davide0707/lora-bidirezionale/pcb/Board Images/Bottom Side PCB.png

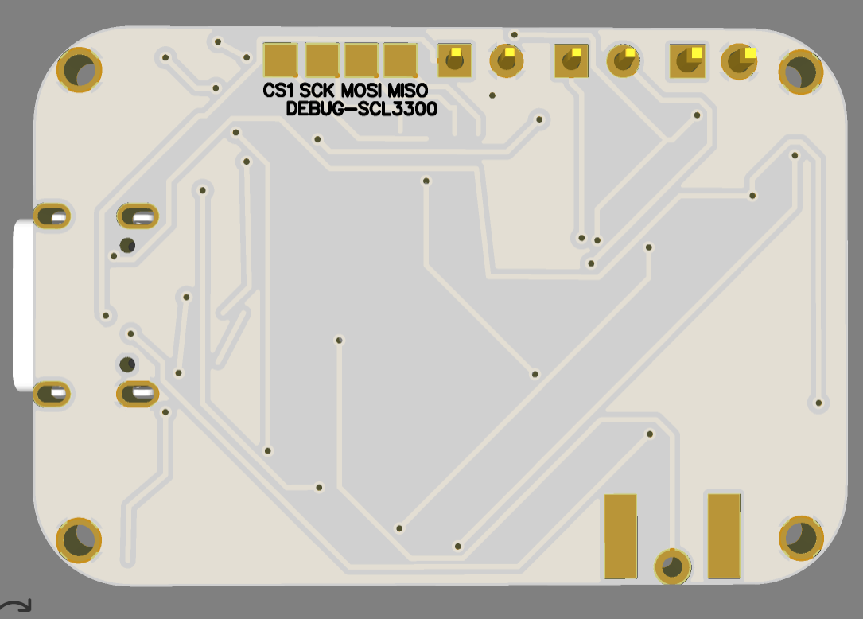
pcb/Board Images/Bottom Side PCB.png
