davide0707/lora-bidirezionale/PROVA PROGETTO/Wio-E5-mini_lorawan_end_node-main/Wio-E5-mini_lorawan_end_node-main/LoRaWAN_End_Node_WIOE5LEmini_FW1_3_1/LoRaWAN/App/lora_app.c

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

/* Includes ------------------------------------------------------------------*/
#include "platform.h"
#include "sys_app.h"
#include "lora_app.h"
#include "stm32_seq.h"
#include "stm32_timer.h"
#include "utilities_def.h"
#include "app_version.h"
#include "lorawan_version.h"
#include "subghz_phy_version.h"
#include "lora_info.h"
#include "LmHandler.h"
#include "adc_if.h"
#include "CayenneLpp.h"
#include "sys_sensors.h"
#include "flash_if.h"


/* USER CODE BEGIN Includes */
#include "scl3300.h"
#include <stdio.h>
#include <string.h>
#include <stdlib.h>
/* USER CODE END Includes */

/* External variables ---------------------------------------------------------*/
/* USER CODE BEGIN EV */
extern SCL3300_t sensor;
#include "lora_app.h"
#include "sys_app.h"
#include "scl3300.h"
#include "usart.h"


float offset_X = 0.0f;
float offset_Y = 0.0f;
float offset_Z = 0.0f;
// Filtro EMA
static float emaX = 0, emaY = 0, emaZ = 0, emaT = 0;
static bool ema_initialized = false;
#define EMA_ALPHA 0.2f  // coefficiente di smoothing (0.1–0.3)

/* USER CODE END EV */

/**
  * @brief LoRa State Machine states
  */
typedef enum TxEventType_e
{
  /**
    * @brief Appdata Transmission issue based on timer every TxDutyCycleTime
    */
  TX_ON_TIMER,
  /**
    * @brief Appdata Transmission external event plugged on OnSendEvent( )
    */
  TX_ON_EVENT
} TxEventType_t;

/**
  * LEDs period value of the timer in ms
  */
#define LED_PERIOD_TIME 500

/**
  * Join switch period value of the timer in ms
  */
#define JOIN_TIME 2000

/*---------------------------------------------------------------------------*/
/*                             LoRaWAN NVM configuration                     */
/*---------------------------------------------------------------------------*/
/**
  * @brief LoRaWAN NVM Flash address
  * @note last 2 sector of a 128kBytes device
  */
#define LORAWAN_NVM_BASE_ADDRESS                    ((void *)0x0803F000UL)

/* USER CODE BEGIN PD */
static const char *slotStrings[] = { "1", "2", "C", "C_MC", "P", "P_MC" };
/* USER CODE END PD */

/**
  * @brief  LoRa End Node send request
  */
static void SendTxData(void);

/**
  * @brief  TX timer callback function
  * @param  context ptr of timer context
  */
static void OnTxTimerEvent(void *context);

/**
  * @brief  join event callback function
  * @param  joinParams status of join
  */
static void OnJoinRequest(LmHandlerJoinParams_t *joinParams);

/**
  * @brief callback when LoRaWAN application has sent a frame
  * @brief  tx event callback function
  * @param  params status of last Tx
  */
static void OnTxData(LmHandlerTxParams_t *params);

/**
  * @brief callback when LoRaWAN application has received a frame
  * @param appData data received in the last Rx
  * @param params status of last Rx
  */
static void OnRxData(LmHandlerAppData_t *appData, LmHandlerRxParams_t *params);

/**
  * @brief callback when LoRaWAN Beacon status is updated
  * @param params status of Last Beacon
  */
static void OnBeaconStatusChange(LmHandlerBeaconParams_t *params);

/**
  * @brief callback when system time has been updated
  */
static void OnSysTimeUpdate(void);

/**
  * @brief callback when LoRaWAN application Class is changed
  * @param deviceClass new class
  */
static void OnClassChange(DeviceClass_t deviceClass);

/**
  * @brief  LoRa store context in Non Volatile Memory
  */
static void StoreContext(void);

/**
  * @brief  stop current LoRa execution to switch into non default Activation mode
  */
static void StopJoin(void);

/**
  * @brief  Join switch timer callback function
  * @param  context ptr of Join switch context
  */
static void OnStopJoinTimerEvent(void *context);

/**
  * @brief  Notifies the upper layer that the NVM context has changed
  * @param  state Indicates if we are storing (true) or restoring (false) the NVM context
  */
static void OnNvmDataChange(LmHandlerNvmContextStates_t state);

/**
  * @brief  Store the NVM Data context to the Flash
  * @param  nvm ptr on nvm structure
  * @param  nvm_size number of data bytes which were stored
  */
static void OnStoreContextRequest(void *nvm, uint32_t nvm_size);

/**
  * @brief  Restore the NVM Data context from the Flash
  * @param  nvm ptr on nvm structure
  * @param  nvm_size number of data bytes which were restored
  */
static void OnRestoreContextRequest(void *nvm, uint32_t nvm_size);

/**
  * Will be called each time a Radio IRQ is handled by the MAC layer
  *
  */
static void OnMacProcessNotify(void);

/**
  * @brief Change the periodicity of the uplink frames
  * @param periodicity uplink frames period in ms
  * @note Compliance test protocol callbacks
  */
static void OnTxPeriodicityChanged(uint32_t periodicity);

/**
  * @brief Change the confirmation control of the uplink frames
  * @param isTxConfirmed Indicates if the uplink requires an acknowledgement
  * @note Compliance test protocol callbacks
  */
static void OnTxFrameCtrlChanged(LmHandlerMsgTypes_t isTxConfirmed);

/**
  * @brief Change the periodicity of the ping slot frames
  * @param pingSlotPeriodicity ping slot frames period in ms
  * @note Compliance test protocol callbacks
  */
static void OnPingSlotPeriodicityChanged(uint8_t pingSlotPeriodicity);

/**
  * @brief Will be called to reset the system
  * @note Compliance test protocol callbacks
  */
static void OnSystemReset(void);

/* USER CODE BEGIN PFP */
/**
  * @brief  LED Tx timer callback function
  * @param  context ptr of LED context
  */
static void OnTxTimerLedEvent(void *context);

/**
  * @brief  LED Rx timer callback function
  * @param  context ptr of LED context
  */
static void OnRxTimerLedEvent(void *context);

/**
  * @brief  LED Join timer callback function
  * @param  context ptr of LED context
  */
static void OnJoinTimerLedEvent(void *context);
/* USER CODE END PFP */

/**
  * @brief LoRaWAN default activation type
  */
static ActivationType_t ActivationType = LORAWAN_DEFAULT_ACTIVATION_TYPE;

/**
  * @brief LoRaWAN force rejoin even if the NVM context is restored
  */
static bool ForceRejoin = LORAWAN_FORCE_REJOIN_AT_BOOT;

/**
  * @brief LoRaWAN handler Callbacks
  */
static LmHandlerCallbacks_t LmHandlerCallbacks =
{
  .GetBatteryLevel =              GetBatteryLevel,
  .GetTemperature =               GetTemperatureLevel,
  .GetUniqueId =                  GetUniqueId,
  .GetDevAddr =                   GetDevAddr,
  .OnRestoreContextRequest =      OnRestoreContextRequest,
  .OnStoreContextRequest =        OnStoreContextRequest,
  .OnMacProcess =                 OnMacProcessNotify,
  .OnNvmDataChange =              OnNvmDataChange,
  .OnJoinRequest =                OnJoinRequest,
  .OnTxData =                     OnTxData,
  .OnRxData =                     OnRxData,
  .OnBeaconStatusChange =         OnBeaconStatusChange,
  .OnSysTimeUpdate =              OnSysTimeUpdate,
  .OnClassChange =                OnClassChange,
  .OnTxPeriodicityChanged =       OnTxPeriodicityChanged,
  .OnTxFrameCtrlChanged =         OnTxFrameCtrlChanged,
  .OnPingSlotPeriodicityChanged = OnPingSlotPeriodicityChanged,
  .OnSystemReset =                OnSystemReset,
};

/**
  * @brief LoRaWAN handler parameters
  */
static LmHandlerParams_t LmHandlerParams =
{
  .ActiveRegion =             ACTIVE_REGION,
  .DefaultClass =             LORAWAN_DEFAULT_CLASS,
  .AdrEnable =                LORAWAN_ADR_STATE,
  .IsTxConfirmed =            LORAWAN_DEFAULT_CONFIRMED_MSG_STATE,
  .TxDatarate =               LORAWAN_DEFAULT_DATA_RATE,
  .TxPower =                  LORAWAN_DEFAULT_TX_POWER,
  .PingSlotPeriodicity =      LORAWAN_DEFAULT_PING_SLOT_PERIODICITY,
  .RxBCTimeout =              LORAWAN_DEFAULT_CLASS_B_C_RESP_TIMEOUT
};

/**
  * @brief Type of Event to generate application Tx
  */
static TxEventType_t EventType = TX_ON_TIMER;

/**
  * @brief Timer to handle the application Tx
  */
static UTIL_TIMER_Object_t TxTimer;

/**
  * @brief Tx Timer period
  */
static UTIL_TIMER_Time_t TxPeriodicity = APP_TX_DUTYCYCLE;

/**
  * @brief Join Timer period
  */
static UTIL_TIMER_Object_t StopJoinTimer;

/* USER CODE BEGIN PV */

/**
  * @brief User application buffer
  */
static uint8_t AppDataBuffer[LORAWAN_APP_DATA_BUFFER_MAX_SIZE];

/**
  * @brief User application data structure
  */
static LmHandlerAppData_t AppData = { 0, 0, AppDataBuffer };

/**
  * @brief Specifies the state of the application LED
  */
static uint8_t AppLedStateOn = RESET;

/**
  * @brief Timer to handle the application Tx Led to toggle
  */
static UTIL_TIMER_Object_t TxLedTimer;

/**
  * @brief Timer to handle the application Rx Led to toggle
  */
static UTIL_TIMER_Object_t RxLedTimer;

/**
  * @brief Timer to handle the application Join Led to toggle
  */
static UTIL_TIMER_Object_t JoinLedTimer;

/* USER CODE END PV */

/* Exported functions ---------------------------------------------------------*/
void LoRaWAN_Init(void)
{
  /* USER CODE BEGIN LoRaWAN_Init_LV */
	uint32_t feature_version = 0UL;
  /* USER CODE END LoRaWAN_Init_LV */

  /* USER CODE BEGIN LoRaWAN_Init_1 */
	/* USER CODE BEGIN LoRaWAN_Init_1 */

	/* MIB_SYSTEM_MAX_RX_ERROR to 200ms Join-response delay */
//	LmHandlerSetSystemMaxRxError(200);

	/* Get LoRaWAN APP version*/
	APP_LOG(TS_OFF, VLEVEL_M, "APPLICATION_VERSION: V%X.%X.%X\r\n",
			(uint8_t)(APP_VERSION_MAIN),
			(uint8_t)(APP_VERSION_SUB1),
			(uint8_t)(APP_VERSION_SUB2));

	/* Get MW LoRaWAN info */
	APP_LOG(TS_OFF, VLEVEL_M, "MW_LORAWAN_VERSION:  V%X.%X.%X\r\n",
			(uint8_t)(LORAWAN_VERSION_MAIN),
			(uint8_t)(LORAWAN_VERSION_SUB1),
			(uint8_t)(LORAWAN_VERSION_SUB2));

	/* Get MW SubGhz_Phy info */
	APP_LOG(TS_OFF, VLEVEL_M, "MW_RADIO_VERSION:    V%X.%X.%X\r\n",
			(uint8_t)(SUBGHZ_PHY_VERSION_MAIN),
			(uint8_t)(SUBGHZ_PHY_VERSION_SUB1),
			(uint8_t)(SUBGHZ_PHY_VERSION_SUB2));

	/* Get LoRaWAN Link Layer info */
	LmHandlerGetVersion(LORAMAC_HANDLER_L2_VERSION, &feature_version);
	APP_LOG(TS_OFF, VLEVEL_M, "L2_SPEC_VERSION:     V%X.%X.%X\r\n",
			(uint8_t)(feature_version >> 24),
			(uint8_t)(feature_version >> 16),
			(uint8_t)(feature_version >> 8));

	/* Get LoRaWAN Regional Parameters info */
	LmHandlerGetVersion(LORAMAC_HANDLER_REGION_VERSION, &feature_version);
	APP_LOG(TS_OFF, VLEVEL_M, "RP_SPEC_VERSION:     V%X-%X.%X.%X\r\n",
			(uint8_t)(feature_version >> 24),
			(uint8_t)(feature_version >> 16),
			(uint8_t)(feature_version >> 8),
			(uint8_t)(feature_version));

	UTIL_TIMER_Create(&TxLedTimer, LED_PERIOD_TIME, UTIL_TIMER_ONESHOT, OnTxTimerLedEvent, NULL);
	UTIL_TIMER_Create(&RxLedTimer, LED_PERIOD_TIME, UTIL_TIMER_ONESHOT, OnRxTimerLedEvent, NULL);
	UTIL_TIMER_Create(&JoinLedTimer, LED_PERIOD_TIME, UTIL_TIMER_PERIODIC, OnJoinTimerLedEvent, NULL);



//	UTIL_TIMER_SetPeriod(&StopJoinTimer, 500);

//	if (FLASH_IF_Init(NULL) != FLASH_IF_OK)
//	{
//		Error_Handler();
//	}

  /* USER CODE END LoRaWAN_Init_1 */

  UTIL_TIMER_Create(&StopJoinTimer, JOIN_TIME, UTIL_TIMER_ONESHOT, OnStopJoinTimerEvent, NULL);

  UTIL_SEQ_RegTask((1 << CFG_SEQ_Task_LmHandlerProcess), UTIL_SEQ_RFU, LmHandlerProcess);

  UTIL_SEQ_RegTask((1 << CFG_SEQ_Task_LoRaSendOnTxTimerOrButtonEvent), UTIL_SEQ_RFU, SendTxData);
  UTIL_SEQ_RegTask((1 << CFG_SEQ_Task_LoRaStoreContextEvent), UTIL_SEQ_RFU, StoreContext);
  UTIL_SEQ_RegTask((1 << CFG_SEQ_Task_LoRaStopJoinEvent), UTIL_SEQ_RFU, StopJoin);

  /* Init Info table used by LmHandler*/
  LoraInfo_Init();

  /* Init the Lora Stack*/
  LmHandlerInit(&LmHandlerCallbacks, APP_VERSION);

  LmHandlerConfigure(&LmHandlerParams);

  /* USER CODE BEGIN LoRaWAN_Init_2 */
  UTIL_TIMER_Start(&JoinLedTimer);
  SCL3300_Init();
  /* USER CODE END LoRaWAN_Init_2 */

  LmHandlerJoin(ActivationType, ForceRejoin);

  if (EventType == TX_ON_TIMER)
  {
    /* send every time timer elapses */
    UTIL_TIMER_Create(&TxTimer, TxPeriodicity, UTIL_TIMER_ONESHOT, OnTxTimerEvent, NULL);
    UTIL_TIMER_Start(&TxTimer);
  }
  else
  {
  }

}

/* USER CODE BEGIN PB_Callbacks */

#if 0 /* User should remove the #if 0 statement and adapt the below code according with his needs*/
void HAL_GPIO_EXTI_Callback(uint16_t GPIO_Pin)
{
  switch (GPIO_Pin)
  {
    case  BUT1_Pin:
      /* Note: when "EventType == TX_ON_TIMER" this GPIO is not initialized */
      if (EventType == TX_ON_EVENT || 1)
      {
        UTIL_SEQ_SetTask((1 << CFG_SEQ_Task_LoRaSendOnTxTimerOrButtonEvent), CFG_SEQ_Prio_0);
      }
      break;
    default:
      break;
  }
}
#endif

/* USER CODE END PB_Callbacks */

static void OnRxData(LmHandlerAppData_t *appData, LmHandlerRxParams_t *params)
{
  /* USER CODE BEGIN OnRxData_1 */
  uint8_t RxPort = 0;

  if (params != NULL)
  {
    UTIL_TIMER_Start(&RxLedTimer);

    if (params->IsMcpsIndication)
    {
      if (appData != NULL)
      {
        RxPort = appData->Port;
        if (appData->Buffer != NULL)
        {
          switch (appData->Port)
          {
            case LORAWAN_SWITCH_CLASS_PORT:
              /*this port switches the class*/
              if (appData->BufferSize == 1)
              {
                switch (appData->Buffer[0])
                {
                  case 0: LmHandlerRequestClass(CLASS_A); break;
                  case 1: LmHandlerRequestClass(CLASS_B); break;
                  case 2: LmHandlerRequestClass(CLASS_C); break;
                  default: break;
                }
              }
              break;

            case LORAWAN_USER_APP_PORT:
              if (appData->BufferSize > 0)
              {
                // copia il payload in una stringa leggibile
                char cmd[64] = {0};
                memcpy(cmd, appData->Buffer, MIN(appData->BufferSize, sizeof(cmd) - 1));

                // rimuovi eventuali spazi o \r\n finali
                for (int i = strlen(cmd) - 1; i >= 0 && (cmd[i] == '\r' || cmd[i] == '\n' || cmd[i] == ' '); i--)
                  cmd[i] = '\0';

                // controlla se il messaggio è "calibrazione"
                if (strcasecmp(cmd, "calibrazione") == 0)
                {
                  APP_LOG(TS_OFF, VLEVEL_M, "Comando ricevuto: calibrazione\r\n");
                  HAL_UART_Transmit(&huart1, (uint8_t *)"==> Avvio calibrazione manuale...\r\n", 36, HAL_MAX_DELAY);

                  Calibra_Offset();

                  HAL_UART_Transmit(&huart1, (uint8_t *)"==> Calibrazione completata.\r\n", 31, HAL_MAX_DELAY);
                }
                else
                {
                  // Se vuoi puoi stampare il comando ricevuto
                  char dbg[80];
                  sprintf(dbg, "Comando non riconosciuto: '%s'\r\n", cmd);
                  HAL_UART_Transmit(&huart1, (uint8_t *)dbg, strlen(dbg), HAL_MAX_DELAY);
                }
              }
              break;

            default:
              break;
          }
        }
      }
    }

    if (params->RxSlot < RX_SLOT_NONE)
    {
      APP_LOG(TS_OFF, VLEVEL_H,
              "###### D/L FRAME:%04d | PORT:%d | DR:%d | SLOT:%s | RSSI:%d | SNR:%d\r\n",
              params->DownlinkCounter, RxPort, params->Datarate,
              slotStrings[params->RxSlot], params->Rssi, params->Snr);
    }
  }
  /* USER CODE END OnRxData_1 */
}


static void SendTxData(void)
{
    LmHandlerErrorStatus_t status = LORAMAC_HANDLER_ERROR;

    if (LmHandlerIsBusy() == false)
    {
        float sumX = 0, sumY = 0, sumZ = 0, sumT = 0;
        int valid = 0;

        // 🔹 10 letture del sensore
        for (int i = 0; i < 10; i++)
        {
            if (Ang_X(&sensor) == 0 && Ang_Y(&sensor) == 0 &&
                Ang_Z(&sensor) == 0 && Temp(&sensor) == 0)
            {
                sumX += (sensor.ANG_X - offset_X);
                sumY += (sensor.ANG_Y - offset_Y);
                sumZ += (sensor.ANG_Z - offset_Z);
                sumT += sensor.TEMP;
                valid++;
            }
            HAL_Delay(100);
        }

        if (valid == 0)
        {
            APP_LOG(TS_ON, VLEVEL_M, "Errore: nessuna lettura valida.\r\n");
            return;
        }

        float avgX = sumX / valid;
        float avgY = sumY / valid;
        float avgZ = sumZ / valid;
        float avgT = sumT / valid;

        // 🔹 Applica il filtro EMA
        if (!ema_initialized) {
            emaX = avgX;
            emaY = avgY;
            emaZ = avgZ;
            emaT = avgT;
            ema_initialized = true;
        } else {
            emaX = EMA_ALPHA * avgX + (1.0f - EMA_ALPHA) * emaX;
            emaY = EMA_ALPHA * avgY + (1.0f - EMA_ALPHA) * emaY;
            emaZ = EMA_ALPHA * avgZ + (1.0f - EMA_ALPHA) * emaZ;
            emaT = EMA_ALPHA * avgT + (1.0f - EMA_ALPHA) * emaT;
        }

        char msg[128];
        sprintf(msg, "%lus:EMA X: %.2f Y: %.2f Z: %.2f T: %.2f\r\n",
                HAL_GetTick()/1000, emaX, emaY, emaZ, emaT);
        HAL_UART_Transmit(&huart1, (uint8_t *)msg, strlen(msg), HAL_MAX_DELAY);


        // 🔹 Prepara pacchetto LoRa con i valori filtrati
        uint8_t *p = AppData.Buffer;
        memcpy(p, &emaX, 4); p += 4;
        memcpy(p, &emaY, 4); p += 4;
        memcpy(p, &emaZ, 4); p += 4;
        memcpy(p, &emaT, 4);

        AppData.BufferSize = 16;
        AppData.Port = LORAWAN_USER_APP_PORT;

        LmHandlerErrorStatus_t status =
            LmHandlerSend(&AppData, LORAMAC_HANDLER_UNCONFIRMED_MSG, false);

        if (status == LORAMAC_HANDLER_SUCCESS){
            APP_LOG(TS_ON, VLEVEL_M, " EMA inviata via LoRa\r\n");
        }else{
            APP_LOG(TS_ON, VLEVEL_M, " Errore invio LoRa (status=%d)\r\n", status);
        }
    }
}


static void OnTxTimerEvent(void *context)
{
  UTIL_SEQ_SetTask((1 << CFG_SEQ_Task_LoRaSendOnTxTimerOrButtonEvent), CFG_SEQ_Prio_0);

  /*Wait for next tx slot*/
  UTIL_TIMER_Start(&TxTimer);
}

/* USER CODE BEGIN PrFD_LedEvents */
static void OnTxTimerLedEvent(void *context)
{
//  HAL_GPIO_WritePin(LED2_GPIO_Port, LED2_Pin, GPIO_PIN_RESET); /* LED_GREEN */
}

static void OnRxTimerLedEvent(void *context)
{
//  HAL_GPIO_WritePin(LED1_GPIO_Port, LED1_Pin, GPIO_PIN_RESET); /* LED_BLUE */
}

static void OnJoinTimerLedEvent(void *context)
{
  HAL_GPIO_TogglePin(LED2_GPIO_Port, LED2_Pin); /* LED_RED LED2*/

}

/* USER CODE END PrFD_LedEvents */

static void OnTxData(LmHandlerTxParams_t *params)
{
  /* USER CODE BEGIN OnTxData_1 */
	  if ((params != NULL))
	  {
	    /* Process Tx event only if its a mcps response to prevent some internal events (mlme) */
	    if (params->IsMcpsConfirm != 0)
	    {
	      //HAL_GPIO_WritePin(LED2_GPIO_Port, LED2_Pin, GPIO_PIN_SET); /* LED_GREEN */
	      UTIL_TIMER_Start(&TxLedTimer);

	      APP_LOG(TS_OFF, VLEVEL_M, "\r\n###### ========== MCPS-Confirm =============\r\n");
	      APP_LOG(TS_OFF, VLEVEL_H, "###### U/L FRAME:%04d | PORT:%d | DR:%d | PWR:%d", params->UplinkCounter,
	              params->AppData.Port, params->Datarate, params->TxPower);

	      APP_LOG(TS_OFF, VLEVEL_H, " | MSG TYPE:");
	      if (params->MsgType == LORAMAC_HANDLER_CONFIRMED_MSG)
	      {
	        APP_LOG(TS_OFF, VLEVEL_H, "CONFIRMED [%s]\r\n", (params->AckReceived != 0) ? "ACK" : "NACK");
	      }
	      else
	      {
	        APP_LOG(TS_OFF, VLEVEL_H, "UNCONFIRMED\r\n");
	      }
	    }
	  }
  /* USER CODE END OnTxData_1 */
}

static void OnJoinRequest(LmHandlerJoinParams_t *joinParams)
{
  /* USER CODE BEGIN OnJoinRequest_1 */
	  if (joinParams != NULL)
	  {
	    if (joinParams->Status == LORAMAC_HANDLER_SUCCESS)
	    {
	      UTIL_SEQ_SetTask((1 << CFG_SEQ_Task_LoRaStoreContextEvent), CFG_SEQ_Prio_0);
	      UTIL_TIMER_Stop(&JoinLedTimer);
//	      HAL_GPIO_WritePin(LED2_GPIO_Port, LED2_Pin, GPIO_PIN_RESET); /* LED_RED */

	      APP_LOG(TS_OFF, VLEVEL_M, "\r\n###### = JOINED = ");
	      if (joinParams->Mode == ACTIVATION_TYPE_ABP)
	      {
	        APP_LOG(TS_OFF, VLEVEL_M, "ABP ======================\r\n");
	      }
	      else
	      {
	        APP_LOG(TS_OFF, VLEVEL_M, "OTAA =====================\r\n");
	      }
	    }
	    else
	    {
	      APP_LOG(TS_OFF, VLEVEL_M, "\r\n###### = JOIN FAILED\r\n");
	      if (joinParams->Mode == ACTIVATION_TYPE_OTAA) {
	    	  APP_LOG(TS_OFF, VLEVEL_M, "\r\n###### = RE-TRYING OTAA JOIN\r\n");
	    	  /* re-try the OTAA join */
	    	  LmHandlerJoin(ActivationType, LORAWAN_FORCE_REJOIN_AT_BOOT);
	      }
	    }
//	    APP_LOG(TS_OFF, VLEVEL_H, "###### U/L FRAME:JOIN | DR:%d | PWR:%d\r\n", joinParams->Datarate, joinParams->TxPower);
	  }
	  if (joinParams->Status == LORAMAC_HANDLER_SUCCESS)
	  {
	      UTIL_SEQ_SetTask((1 << CFG_SEQ_Task_LoRaStoreContextEvent), CFG_SEQ_Prio_0);
	      UTIL_TIMER_Stop(&JoinLedTimer);
	      APP_LOG(TS_OFF, VLEVEL_M, "Device joined LoRa network!\r\n");

	      // 🔹 Calibrazione del sensore una sola volta
	      Calibra_Offset();

	      // 🔹 Avvio raccolta dati e invio media
	      UTIL_SEQ_SetTask((1 << CFG_SEQ_Task_LoRaSendOnTxTimerOrButtonEvent), CFG_SEQ_Prio_0);
	  }

  /* USER CODE END OnJoinRequest_1 */
}

static void OnBeaconStatusChange(LmHandlerBeaconParams_t *params)
{
  /* USER CODE BEGIN OnBeaconStatusChange_1 */
	  if (params != NULL)
	  {
	    switch (params->State)
	    {
	      default:
	      case LORAMAC_HANDLER_BEACON_LOST:
	      {
	        APP_LOG(TS_OFF, VLEVEL_M, "\r\n###### BEACON LOST\r\n");
	        break;
	      }
	      case LORAMAC_HANDLER_BEACON_RX:
	      {
	        APP_LOG(TS_OFF, VLEVEL_M,
	                "\r\n###### BEACON RECEIVED | DR:%d | RSSI:%d | SNR:%d | FQ:%d | TIME:%d | DESC:%d | "
	                "INFO:02X%02X%02X %02X%02X%02X\r\n",
	                params->Info.Datarate, params->Info.Rssi, params->Info.Snr, params->Info.Frequency,
	                params->Info.Time.Seconds, params->Info.GwSpecific.InfoDesc,
	                params->Info.GwSpecific.Info[0], params->Info.GwSpecific.Info[1],
	                params->Info.GwSpecific.Info[2], params->Info.GwSpecific.Info[3],
	                params->Info.GwSpecific.Info[4], params->Info.GwSpecific.Info[5]);
	        break;
	      }
	      case LORAMAC_HANDLER_BEACON_NRX:
	      {
	        APP_LOG(TS_OFF, VLEVEL_M, "\r\n###### BEACON NOT RECEIVED\r\n");
	        break;
	      }
	    }
	  }
  /* USER CODE END OnBeaconStatusChange_1 */
}

static void OnSysTimeUpdate(void)
{
}

static void OnClassChange(DeviceClass_t deviceClass)
{
  /* USER CODE BEGIN OnClassChange_1 */
	  APP_LOG(TS_OFF, VLEVEL_M, "Switch to Class %c done\r\n", "ABC"[deviceClass]);
  /* USER CODE END OnClassChange_1 */
}

static void OnMacProcessNotify(void)
{
  UTIL_SEQ_SetTask((1 << CFG_SEQ_Task_LmHandlerProcess), CFG_SEQ_Prio_0);

}

static void OnTxPeriodicityChanged(uint32_t periodicity)
{
  TxPeriodicity = periodicity;

  if (TxPeriodicity == 0)
  {
    /* Revert to application default periodicity */
    TxPeriodicity = APP_TX_DUTYCYCLE;
  }

  /* Update timer periodicity */
  UTIL_TIMER_Stop(&TxTimer);
  UTIL_TIMER_SetPeriod(&TxTimer, TxPeriodicity);
  UTIL_TIMER_Start(&TxTimer);
}

static void OnTxFrameCtrlChanged(LmHandlerMsgTypes_t isTxConfirmed)
{
  LmHandlerParams.IsTxConfirmed = isTxConfirmed;
}

static void OnPingSlotPeriodicityChanged(uint8_t pingSlotPeriodicity)
{
  LmHandlerParams.PingSlotPeriodicity = pingSlotPeriodicity;
}

static void OnSystemReset(void)
{
  if ((LORAMAC_HANDLER_SUCCESS == LmHandlerHalt()) && (LmHandlerJoinStatus() == LORAMAC_HANDLER_SET))
  {
    NVIC_SystemReset();
  }
}

static void StopJoin(void)
{
  /* USER CODE BEGIN StopJoin_1 */
	  HAL_GPIO_WritePin(LED2_GPIO_Port, LED2_Pin, GPIO_PIN_SET); /* LED_RED */
  /* USER CODE END StopJoin_1 */

  UTIL_TIMER_Stop(&TxTimer);

  if (LORAMAC_HANDLER_SUCCESS != LmHandlerStop())
  {
    APP_LOG(TS_OFF, VLEVEL_M, "LmHandler Stop on going ...\r\n");
  }
  else
  {
    APP_LOG(TS_OFF, VLEVEL_M, "LmHandler Stopped\r\n");
    if (LORAWAN_DEFAULT_ACTIVATION_TYPE == ACTIVATION_TYPE_ABP)
    {
      ActivationType = ACTIVATION_TYPE_OTAA;
      APP_LOG(TS_OFF, VLEVEL_M, "LmHandler switch to OTAA mode\r\n");
    }
    else
    {
      ActivationType = ACTIVATION_TYPE_ABP;
      APP_LOG(TS_OFF, VLEVEL_M, "LmHandler switch to ABP mode\r\n");
    }
    LmHandlerConfigure(&LmHandlerParams);
    LmHandlerJoin(ActivationType, true);
    UTIL_TIMER_Start(&TxTimer);
  }
  UTIL_TIMER_Start(&StopJoinTimer);
}

static void OnStopJoinTimerEvent(void *context)
{
  if (ActivationType == LORAWAN_DEFAULT_ACTIVATION_TYPE)
  {
    UTIL_SEQ_SetTask((1 << CFG_SEQ_Task_LoRaStopJoinEvent), CFG_SEQ_Prio_0);
  }
  /* USER CODE BEGIN OnStopJoinTimerEvent_Last */
  HAL_GPIO_WritePin(LED2_GPIO_Port, LED2_Pin, GPIO_PIN_RESET); /* LED_RED */
  /* USER CODE END OnStopJoinTimerEvent_Last */
}

static void StoreContext(void)
{
  LmHandlerErrorStatus_t status = LORAMAC_HANDLER_ERROR;

  status = LmHandlerNvmDataStore();

  if (status == LORAMAC_HANDLER_NVM_DATA_UP_TO_DATE)
  {
    APP_LOG(TS_OFF, VLEVEL_M, "NVM DATA UP TO DATE\r\n");
  }
  else if (status == LORAMAC_HANDLER_ERROR)
  {
    APP_LOG(TS_OFF, VLEVEL_M, "NVM DATA STORE FAILED\r\n");
  }
}

static void OnNvmDataChange(LmHandlerNvmContextStates_t state)
{
  if (state == LORAMAC_HANDLER_NVM_STORE)
  {
    APP_LOG(TS_OFF, VLEVEL_M, "NVM DATA STORED\r\n");
  }
  else
  {
    APP_LOG(TS_OFF, VLEVEL_M, "NVM DATA RESTORED\r\n");
  }
}

static void OnStoreContextRequest(void *nvm, uint32_t nvm_size)
{
  /* store nvm in flash */
  if (FLASH_IF_Erase(LORAWAN_NVM_BASE_ADDRESS, FLASH_PAGE_SIZE) == FLASH_IF_OK)
  {
    FLASH_IF_Write(LORAWAN_NVM_BASE_ADDRESS, (const void *)nvm, nvm_size);
  }
}

static void OnRestoreContextRequest(void *nvm, uint32_t nvm_size)
{
  FLASH_IF_Read(nvm, LORAWAN_NVM_BASE_ADDRESS, nvm_size);
}
