davide0707/lora-bidirezionale/PROVA PROGETTO/Wio-E5-mini_lorawan_end_node-main/Wio-E5-mini_lorawan_end_node-main/LoRaWAN_End_Node_WIOE5LEmini_FW1_3_1/Core/Inc/sys_debug.h

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

/* Define to prevent recursive inclusion -------------------------------------*/
#ifndef __SYS_DEBUG_H__
#define __SYS_DEBUG_H__

#ifdef __cplusplus
extern "C" {
#endif

/* Includes ------------------------------------------------------------------*/
#include "sys_conf.h"
#include "platform.h"

/* Exported types ------------------------------------------------------------*/
/* Exported constants --------------------------------------------------------*/
/* Pin defines */

/**  Definition for Probe Line 1   **/
/**
  * @brief Pin of Probe Line 1
  */
#define PROBE_LINE1_PIN                           GPIO_PIN_0

/**
  * @brief Port of Probe Line 1
  */
#define PROBE_LINE1_PORT                          GPIOA

/**
  * @brief Enable GPIOs clock of Probe Line 1
  */
#define PROBE_LINE1_CLK_ENABLE()                  __HAL_RCC_GPIOA_CLK_ENABLE()

/**
  * @brief Disable GPIOs clock of Probe Line 1
  */
#define PROBE_LINE1_CLK_DISABLE()                 __HAL_RCC_GPIOA_CLK_DISABLE()

/**  Definition for Probe Line 2   **/
/**
  * @brief Pin of Probe Line 2
  */
#define PROBE_LINE2_PIN                           GPIO_PIN_10

/**
  * @brief Port of Probe Line 2
  */
#define PROBE_LINE2_PORT                          GPIOB

/**
  * @brief Enable GPIOs clock of Probe Line 2
  */
#define PROBE_LINE2_CLK_ENABLE()                  __HAL_RCC_GPIOB_CLK_ENABLE()

/**
  * @brief Disable GPIOs clock of Probe Line 2
  */
#define PROBE_LINE2_CLK_DISABLE()                 __HAL_RCC_GPIOB_CLK_DISABLE()

/**  Definition for Probe Line 3   **/
/**
  * @brief Pin of Probe Line 3
  */
#define PROBE_LINE3_PIN                           GPIO_PIN_3

/**
  * @brief Port of Probe Line 3
  */
#define PROBE_LINE3_PORT                          GPIOB

/**
  * @brief Enable GPIOs clock of Probe Line 3
  */
#define PROBE_LINE3_CLK_ENABLE()                  __HAL_RCC_GPIOB_CLK_ENABLE()

/**
  * @brief Disable GPIOs clock of Probe Line 3
  */
#define PROBE_LINE3_CLK_DISABLE()                 __HAL_RCC_GPIOB_CLK_DISABLE()

/**  Definition for Probe Line 4   **/
/**
  * @brief Pin of Probe Line 4
  */
#define PROBE_LINE4_PIN                           GPIO_PIN_4

/**
  * @brief Port of Probe Line 4
  */
#define PROBE_LINE4_PORT                          GPIOB

/**
  * @brief Enable GPIOs clock of Probe Line 4
  */
#define PROBE_LINE4_CLK_ENABLE()                  __HAL_RCC_GPIOB_CLK_ENABLE()

/**
  * @brief Disable GPIOs clock of Probe Line 4
  */
#define PROBE_LINE4_CLK_DISABLE()                 __HAL_RCC_GPIOB_CLK_DISABLE()

/* External variables --------------------------------------------------------*/
/* Exported macro ------------------------------------------------------------*/
#if !defined (DISABLE_PROBE_GPIO)

/**
  * @brief Set pin to x value
  */
#define PROBE_GPIO_WRITE( gpio, n, x )     HAL_GPIO_WritePin( gpio, n, (GPIO_PinState)(x) )

/**
  * @brief Set pin to high level
  */
#define PROBE_GPIO_SET_LINE( gpio, n )     LL_GPIO_SetOutputPin( gpio, n )

/**
  * @brief Set pin to low level
  */
#define PROBE_GPIO_RST_LINE( gpio, n )     LL_GPIO_ResetOutputPin( gpio, n )

#else  /* DISABLE_PROBE_GPIO */

/**
  * @brief not usable
  */
#define PROBE_GPIO_WRITE( gpio, n, x )

/**
  * @brief not usable
  */
#define PROBE_GPIO_SET_LINE( gpio, n )

/**
  * @brief not usable
  */
#define PROBE_GPIO_RST_LINE( gpio, n )

#endif /* DISABLE_PROBE_GPIO */

/* Exported functions prototypes ---------------------------------------------*/
/**
  * @brief Initializes the SW probes pins and the monitor RF pins via Alternate Function
  */
void DBG_Init(void);

#ifdef __cplusplus
}
#endif

#endif /* __SYS_DEBUG_H__ */
